bkuhn4/golf-gps/src/sw/main/bitmaps.cpp

// bitmaps.cpp
#include "bitmaps.h"
#include <Arduino.h>

// --- MENU ITEMS BITMAP DATA ---
// 'battery_icon', 16x16px
const unsigned char epd_bitmap_battery_icon[] PROGMEM = {
  0x00, 0x00, 0xc0, 0x03, 0xc0, 0x03, 0xf0, 0x0f, 0x10, 0x08, 0xd0, 0x0b, 0xd0, 0x0b, 0x10, 0x08,
  0xd0, 0x0b, 0xd0, 0x0b, 0x10, 0x08, 0xd0, 0x0b, 0xd0, 0x0b, 0x10, 0x08, 0xf0, 0x0f, 0x00, 0x00
};
// 'folder_icon', 16x16px
const unsigned char epd_bitmap_folder_icon[] PROGMEM = {
  0x00, 0x00, 0x3f, 0x00, 0xe1, 0x3f, 0x01, 0x20, 0x01, 0x20, 0x01, 0xff, 0x81, 0x80, 0x7d, 0x80,
  0x05, 0x80, 0x03, 0x40, 0x03, 0x40, 0x03, 0x20, 0xff, 0x3f, 0x00, 0x00, 0x00, 0x00, 0x00, 0x00
};
// 'gps_icon', 16x16px
const unsigned char epd_bitmap_gps_icon[] PROGMEM = {
  0x38, 0x00, 0x04, 0x00, 0x32, 0x00, 0x09, 0x30, 0x25, 0x48, 0x15, 0x84, 0x80, 0x83, 0xc0, 0x43,
  0xc0, 0x27, 0xc0, 0x1f, 0x20, 0x1f, 0x10, 0x1e, 0x08, 0x0e, 0x08, 0x01, 0x90, 0x00, 0x60, 0x00
};
// 'location_icon', 16x16px
const unsigned char epd_bitmap_location_icon[] PROGMEM = {
  0xc0, 0x07, 0x60, 0x0c, 0xb0, 0x1b, 0xd0, 0x17, 0xd0, 0x17, 0xd0, 0x17, 0xf0, 0x1f, 0xe0, 0x0f,
  0xc0, 0x07, 0x80, 0x03, 0x80, 0x03, 0x80, 0x03, 0x00, 0x01, 0x00, 0x01, 0x00, 0x01, 0x00, 0x00
};
// 'placeholder_icon', 16x16px
const unsigned char epd_bitmap_placeholder_icon[] PROGMEM = {
  0x00, 0x00, 0x00, 0x00, 0xf0, 0x07, 0xf0, 0x0f, 0x30, 0x0c, 0x30, 0x0c, 0x30, 0x0c, 0xf0, 0x0f,
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
	0x00, 0x00, 0x00, 0x00, 0x00, 0x00, 0x3e, 0x00, 0x66, 0x00, 0x66, 0x66, 0x66, 0x76, 0x66, 0x0e, 
	0x66, 0x06, 0x66, 0x06, 0x66, 0x06, 0x3e, 0x06, 0x00, 0x00, 0x00, 0x00, 0x00, 0x00, 0x00, 0x00
};
// 'sw_icon', 16x16px
const unsigned char epd_bitmap_sw_icon [] PROGMEM = {
	0x00, 0x00, 0x00, 0x00, 0x00, 0x00, 0x1e, 0x63, 0x33, 0x63, 0x03, 0x6b, 0x03, 0x6b, 0x1e, 0x6b, 
	0x30, 0x6b, 0x30, 0x6b, 0x33, 0x6b, 0x1e, 0x36, 0x00, 0x00, 0x00, 0x00, 0x00, 0x00, 0x00, 0x00
};
// 'pw_icon', 16x16px
const unsigned char epd_bitmap_pw_icon [] PROGMEM = {
	0x00, 0x00, 0x00, 0x00, 0x00, 0x00, 0x1f, 0x63, 0x33, 0x63, 0x33, 0x6b, 0x33, 0x6b, 0x1f, 0x6b, 
	0x03, 0x6b, 0x03, 0x6b, 0x03, 0x6b, 0x03, 0x36, 0x00, 0x00, 0x00, 0x00, 0x00, 0x00, 0x00, 0x00
};
