bkuhn4/golf-gps/src/sw/main/gps.h

#ifndef GPS_H
#define GPS_H

#include <Arduino.h>
#include <Wire.h>
#include <SparkFun_u-blox_GNSS_v3.h>

// Pin Definitions
#define GPS_EN_N_PIN 3
#define GPS_RESET_N_PIN 21

// Configuration
#define GPS_UPDATE_RATE_HZ 25

class GpsHandler {
public:
    GpsHandler();
    bool begin();
    
    // Main loop update - call this frequently to poll the GPS
    bool update();

    // Data Getters (return cached values)
    int32_t getLatitude();
    int32_t getLongitude();
    byte getSIV(); // Satellites In View
    bool isLocked(); // Check if we have a valid fix
    
    // Time and Date
    // Returns time as HHMMSS
    uint32_t getTime();
    // Returns date as DDMMYY
    uint32_t getDate();

    // Hardware Reset
    void reset();
    
    // Distance Calculation (Vincenty Formula)
    // Returns distance in meters between two coordinates (in decimal degrees)
    double calculateDistanceVincenty(double lat1, double lon1, double lat2, double lon2);
    
    // Direct access to the GNSS object if needed
    SFE_UBLOX_GNSS myGNSS;

private:
    int32_t _latitude;
    int32_t _longitude;
    byte _siv;
    byte _fixType;
    uint32_t _time;
    uint32_t _date;
};

#endif // GPS_H
